HomeBusProjects/furball/src/hw.h

// hardware-related definitions
#define PIR_PIN    33
#define SOUND_PIN  39
#define BUTTON_PIN 35

#define LED_RED    12
#define LED_GREEN  13
#define LED_BLUE   14

#define PMS_RX_PIN  15
#define PMS_TX_PIN  16

#include <HTTPClient.h>
#include <WiFiClient.h>
#include <WiFiClientSecure.h>
